tanj299/synthesis/sensor_tests/light_test_schematic.png

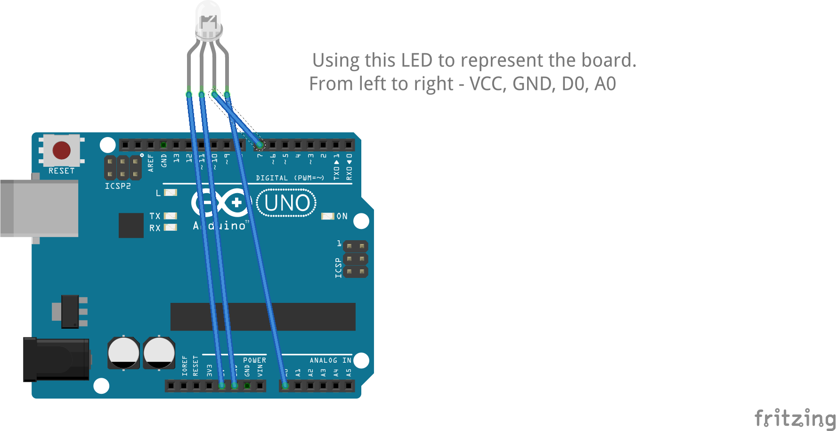
sensor_tests/light_test_schematic.png
