tanj299/synthesis/sensor_tests/pump_relay_test_schematic.png

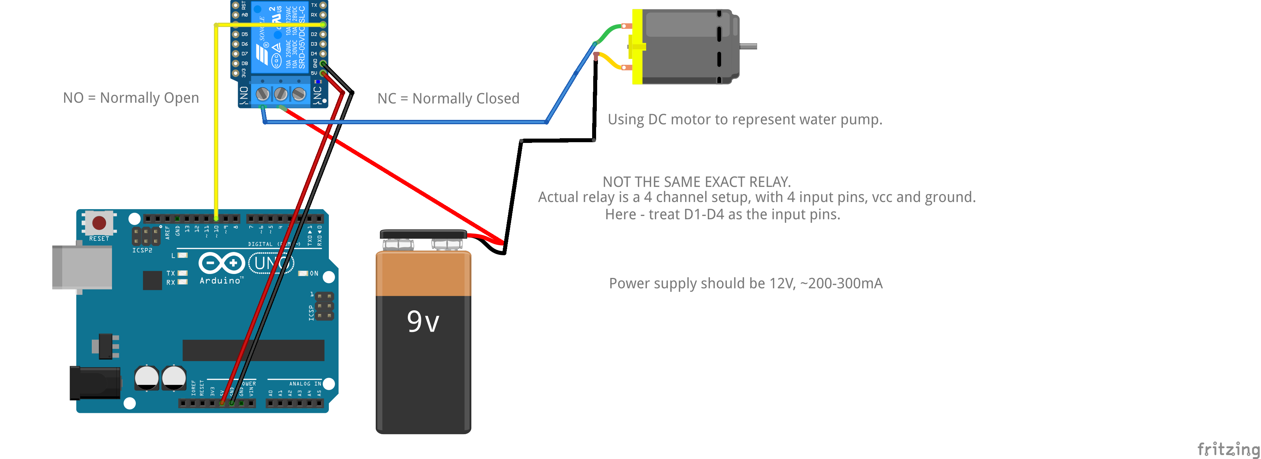
sensor_tests/pump_relay_test_schematic.png
