tanj299/synthesis/sensor_tests/soil_moisture_test_schematic.png

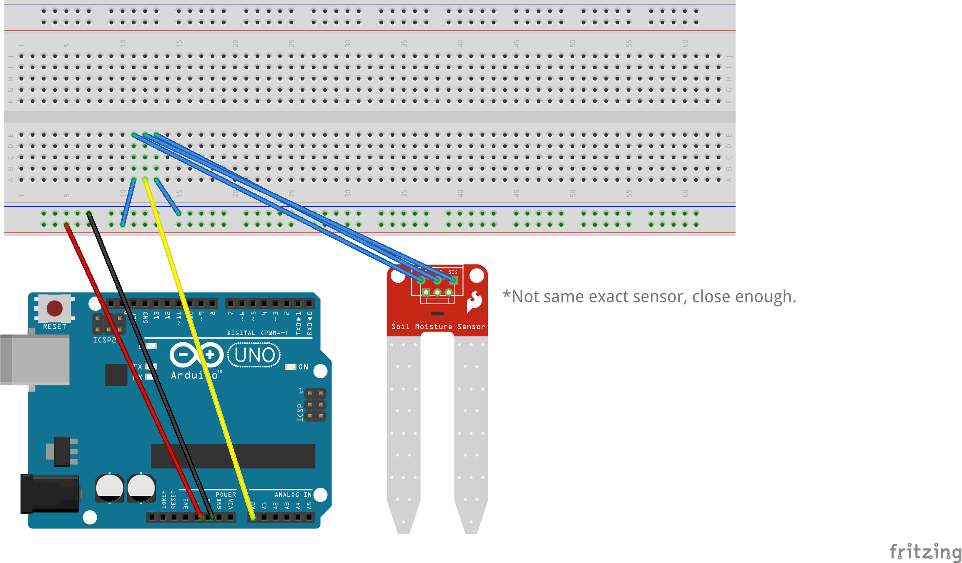
sensor_tests/soil_moisture_test_schematic.png
