tanj299/synthesis/sensor_tests/soil_temp_test_schematic.png

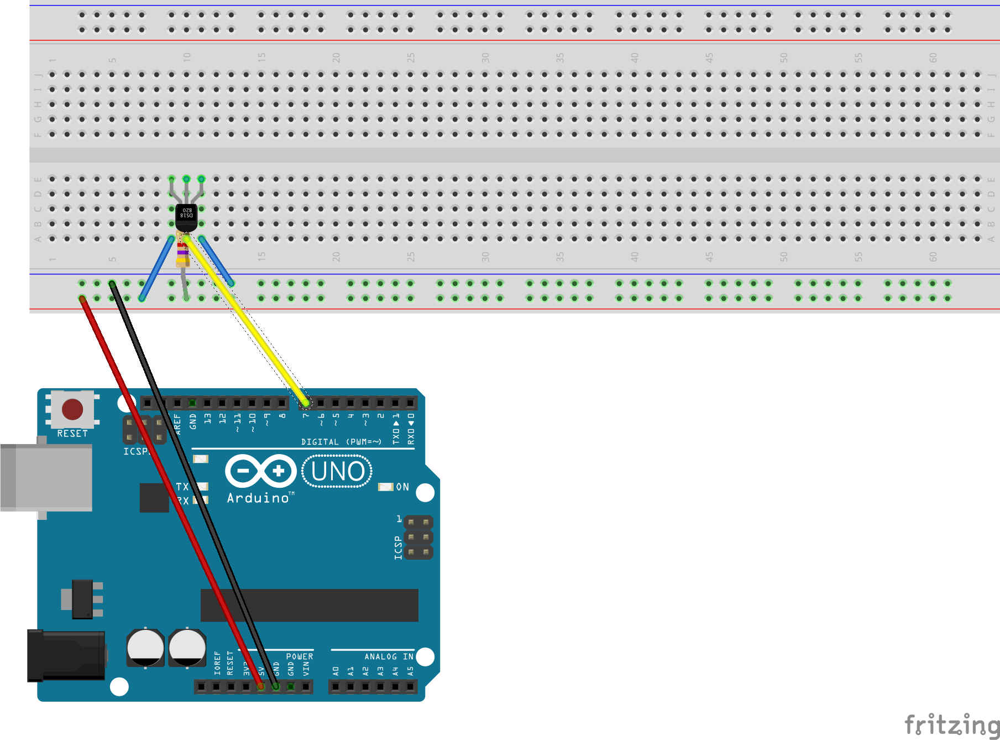
sensor_tests/soil_temp_test_schematic.png
