tanj299/synthesis/sensor_tests/water_level_test_schematic.png

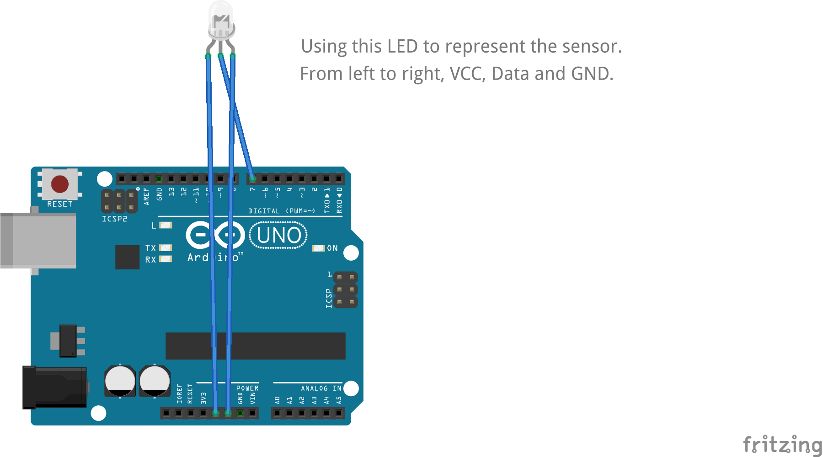
sensor_tests/water_level_test_schematic.png
